SuperMakeSomething/diy-stream-deck/Arduino Libraries/LCDWIKI_KBV/Example/Example_07_show_bmp_picture/show_bmp_picture/PIC_320x480/01.bmp

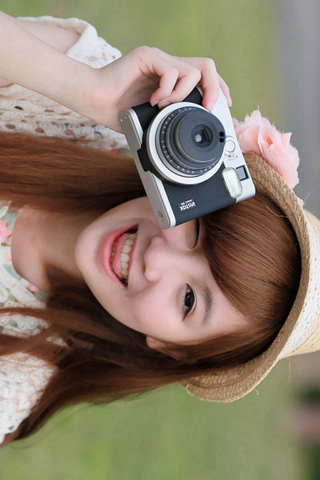
Arduino Libraries/LCDWIKI_KBV/Example/Example_07_show_bmp_picture/show_bmp_picture/PIC_320x480/01.bmp
