SuperMakeSomething/diy-stream-deck/Arduino Libraries/LCDWIKI_KBV/lcd_mode.h

#ifndef _lcd_mode_
#define _lcd_mode_

//if using 8bit mode,set the below macro definition to 1
//if using 16bit mode,set the below macro definition to 0
#define CONFIG_USE_8BIT_BUS 1

//if using 8bit mode on Mega2560 and the data pin is from 22 to 29,please uncomment the below macro definition
//if using 8bit mode on UNO and the data pin is from 2 to 9,please comment the below macro definition
//#define USE_8BIT_SHIELD_ON_MEGA 

#endif // _mcu_pin_magic_
